solarcaratuva/PowerSystem/1N5819.spice

**************************************
*      Model Generated by MODPEX     *
*Copyright(c) Symmetry Design Systems*
*         All Rights Reserved        *
*    UNPUBLISHED LICENSED SOFTWARE   *
*   Contains Proprietary Information *
*      Which is The Property of      *
*     SYMMETRY OR ITS LICENSORS      *
*Commercial Use or Resale Restricted *
*   by Symmetry License Agreement    *
**************************************
* Model generated on Aug 21, 00
* MODEL FORMAT: PSpice
.MODEL D1n5819 d
+IS=1.19279e-05 RS=0.0625421 N=1.16517 EG=1.3
+XTI=3.22098 BV=40 IBV=0.001 CJO=1.50114e-10
+VJ=1.5 M=0.590203 FC=0.5 TT=2.6273e-08
+KF=0 AF=1
